pszafer/boneIO/Case/spacer_relay_24x16A.stl

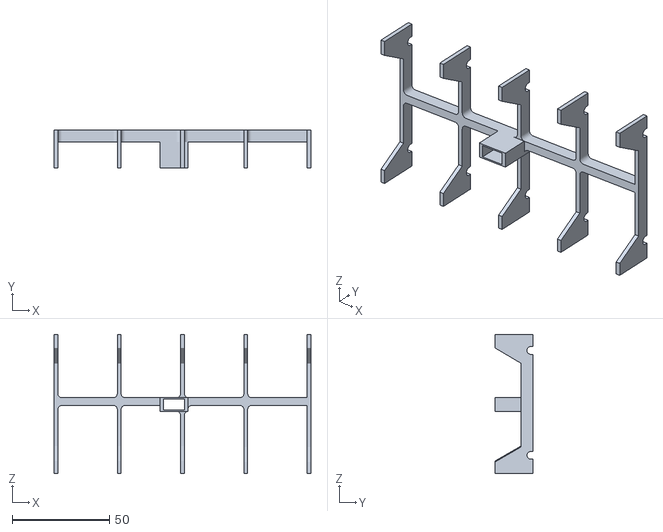
[picture p20: CAD file, 2021-12-29, last stored version]
Case/spacer_relay_24x16A.stl
132.1 x 19.3 x 71.5
