pszafer/boneIO/Circuit/boneIO - input board_BBB/3D_model/CR1220_VCNK.stp

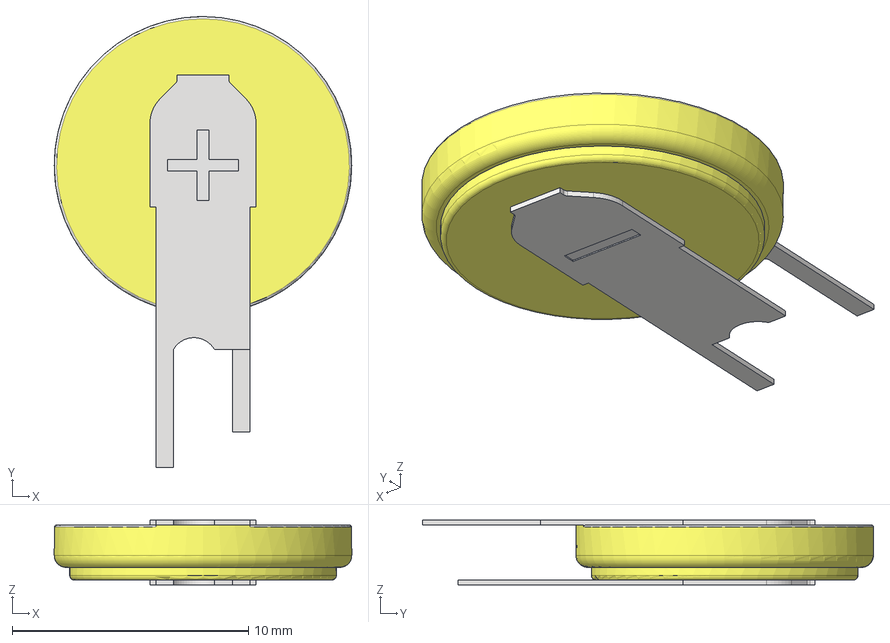
[picture p21: CAD file, 2021-11-15, last stored version]
Circuit/boneIO - input board_BBB/3D_model/CR1220_VCNK.stp
12.6 x 19.1 x 2.74 mm
