pszafer/boneIO/Circuit/boneIO - input board_ESP/3D/ESP32.STEP

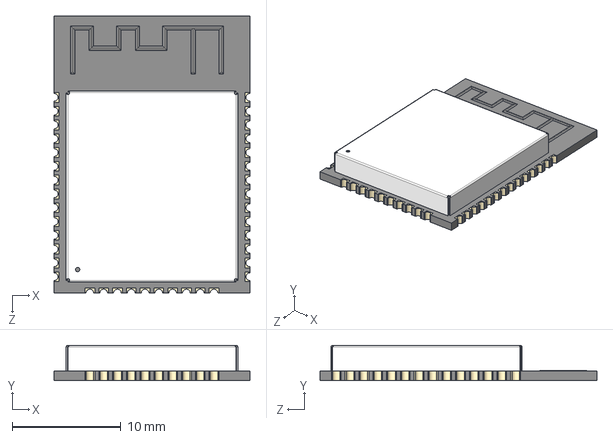
[picture p22: CAD file, 2021-12-20, last stored version]
Circuit/boneIO - input board_ESP/3D/ESP32.STEP
18.0 x 3.25 x 25.5 mm
