pszafer/boneIO/Case/spacer_relay_32x5A.stl

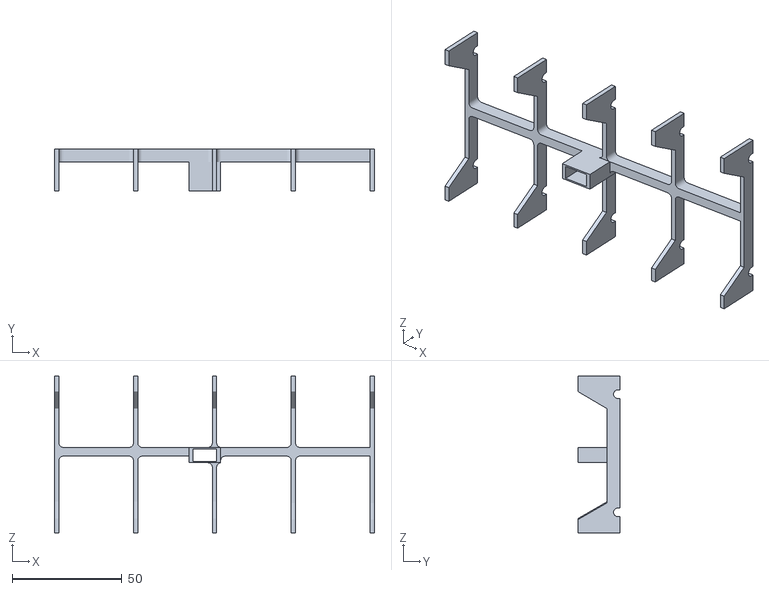
[picture p23: CAD file, 2021-12-29, last stored version]
Case/spacer_relay_32x5A.stl
146.0 x 19.3 x 71.5
