pszafer/boneIO/Circuit/boneIO - input board_ESP/3D/Connector_1Port_RJ45.step

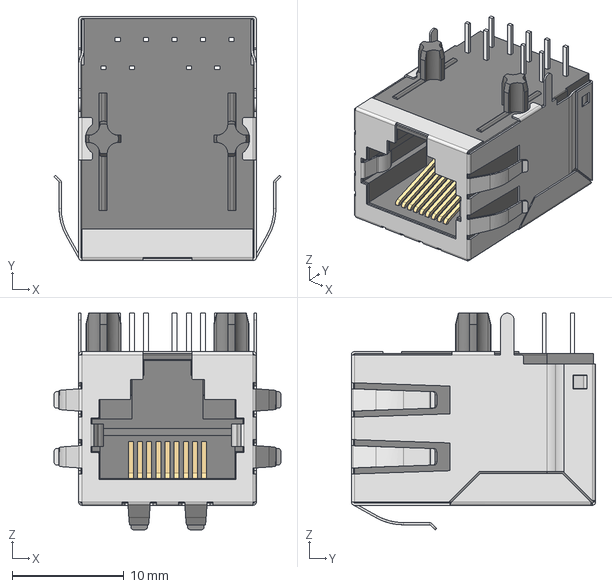
[picture p24: CAD file, 2021-12-20, last stored version]
Circuit/boneIO - input board_ESP/3D/Connector_1Port_RJ45.step
20.3 x 21.8 x 19.4 mm
insulator
shielding
