pszafer/boneIO/Case/lock_pin.stl

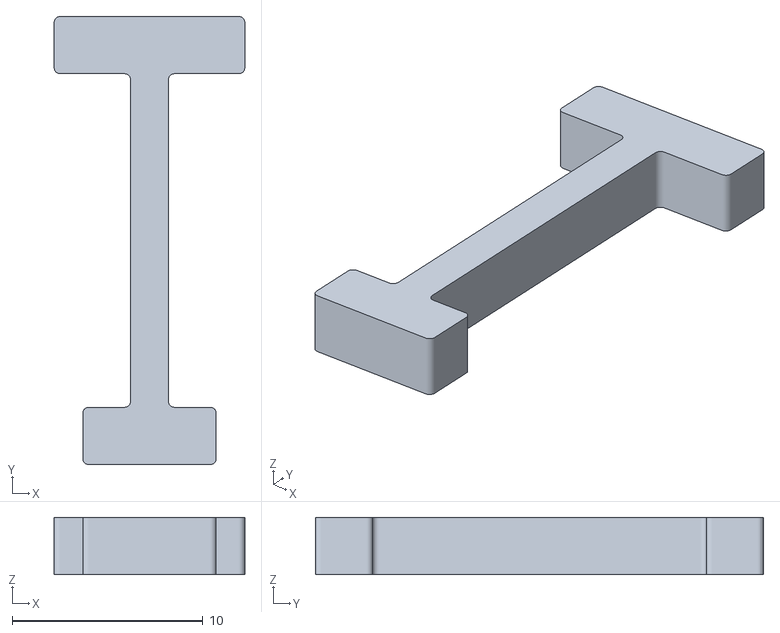
[picture p25: CAD file, 2021-12-29, last stored version]
Case/lock_pin.stl
10.0 x 23.5 x 3.00
