pszafer/boneIO/Case/boneIO-distance-relay-32x5.stl

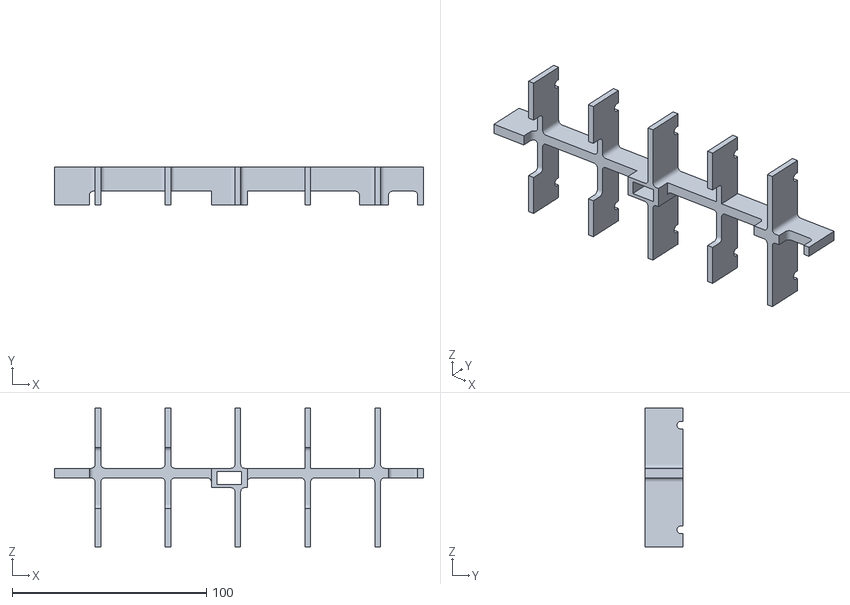
[picture p26: CAD file, 2021-12-07, last stored version]
Case/boneIO-distance-relay-32x5.stl
190.0 x 19.4 x 71.5
