pszafer/boneIO/Case/clips.stl

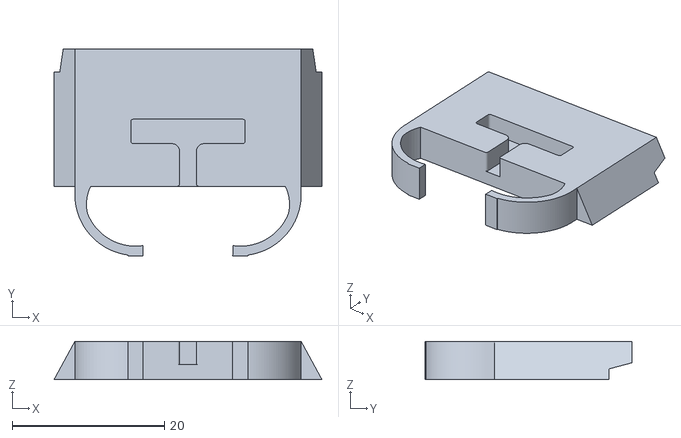
[picture p27: CAD file, 2021-12-07, last stored version]
Case/clips.stl
35.2 x 27.1 x 5.00
