pszafer/boneIO/Case/boneIO-button-distance-relay-32x5A.stp

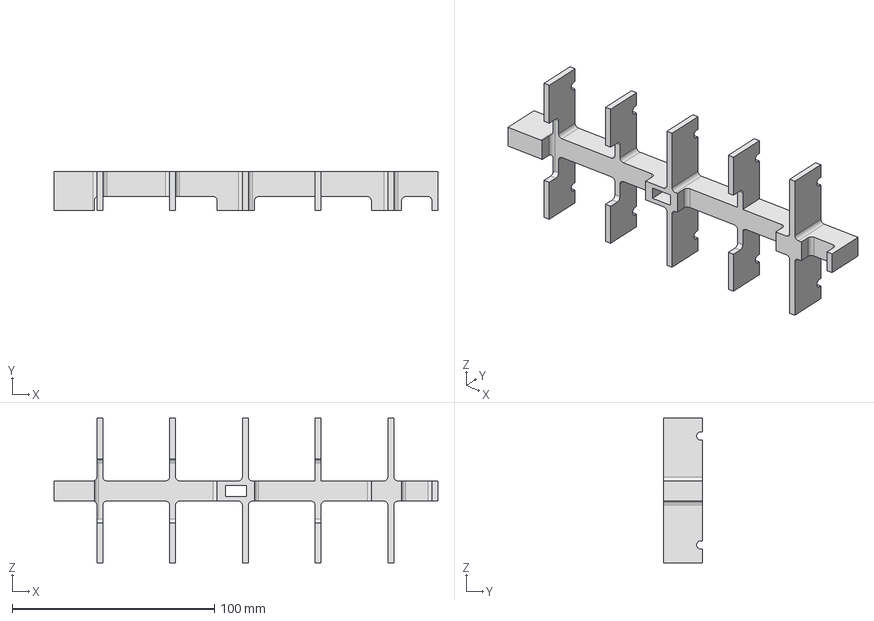
[picture p28: CAD file, 2021-11-15, last stored version]
Case/boneIO-button-distance-relay-32x5A.stp
190.0 x 19.4 x 71.5 mm
