pszafer/boneIO/Case/boneIO-button-distance-relay-24x16A.stp

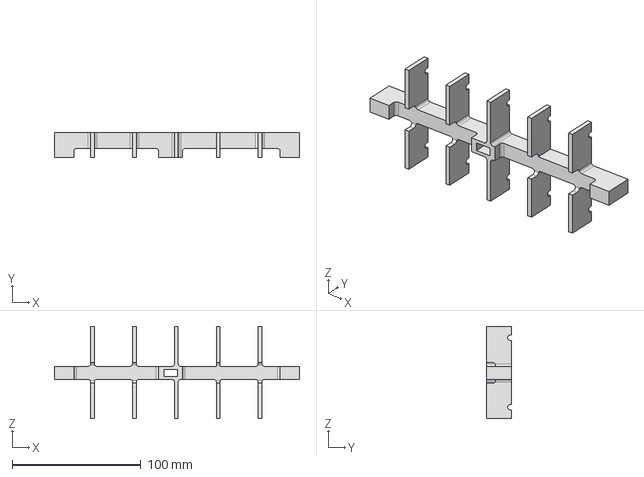
[picture p29: CAD file, 2021-11-15, last stored version]
Case/boneIO-button-distance-relay-24x16A.stp
190.0 x 19.4 x 71.5 mm
