pszafer/boneIO/.resources/boneIO_v0.2_assembly.jpg

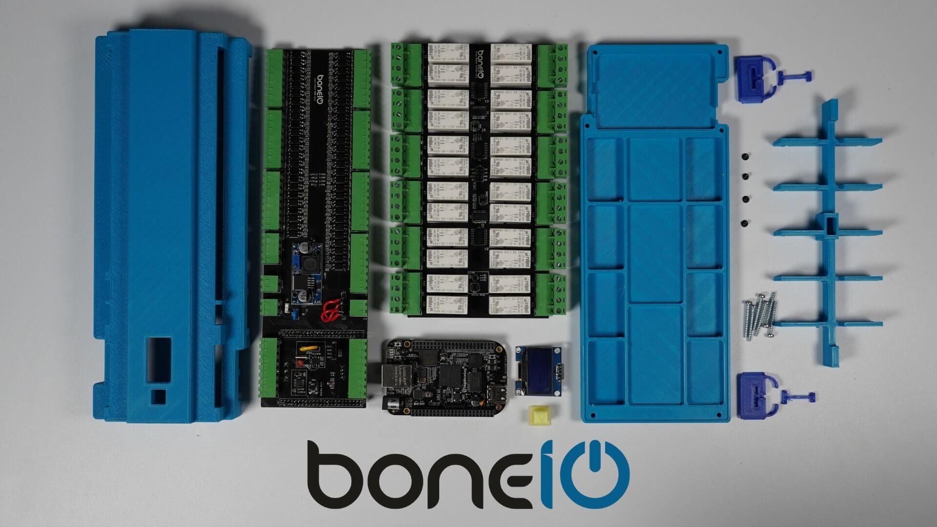
.resources/boneIO_v0.2_assembly.jpg
